mtnbikeray/Incidence-Deflection-Gauge/incidence.jpeg

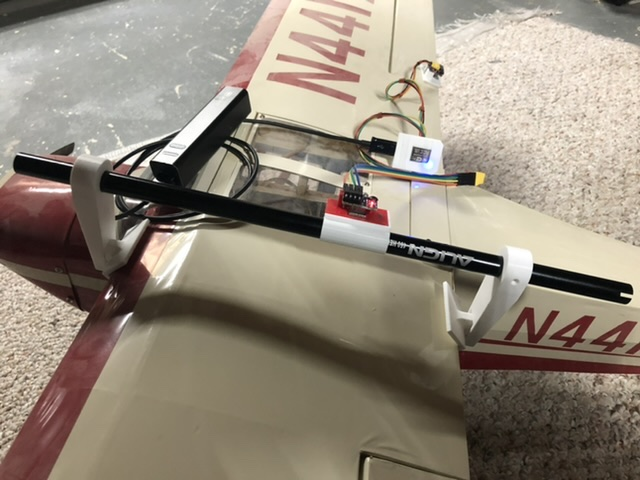
incidence.jpeg
